ene9ba/IoT-3D-Printer-Control/Hardware/Cabinetcontrol1/Step/IRLML2402TRPBF.stp

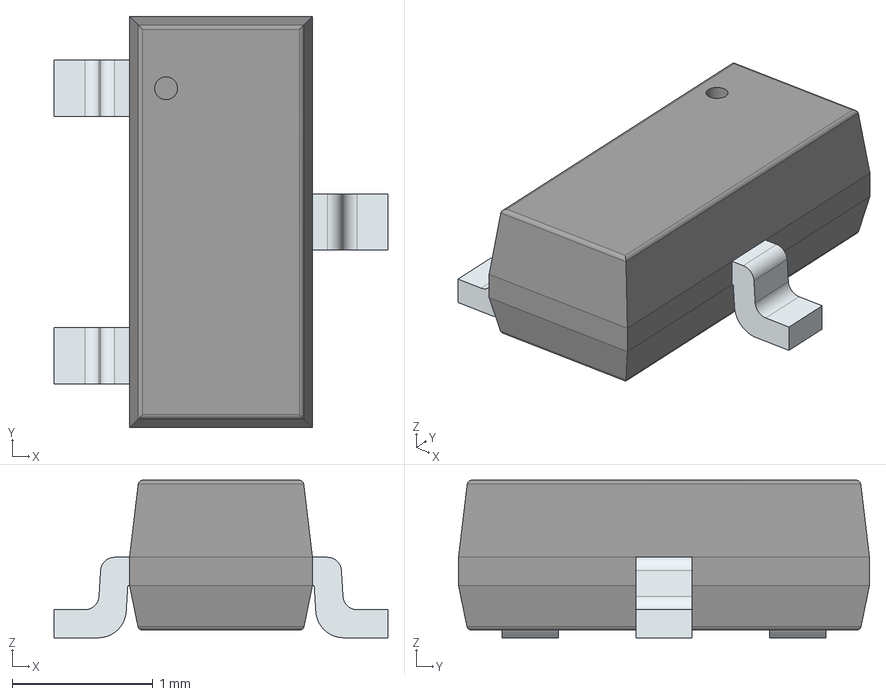
[picture p22: CAD file, 2024-01-27]
Hardware/Cabinetcontrol1/Step/IRLML2402TRPBF.stp
2.37 x 2.92 x 1.12 mm
PinsArrayL
FilletPinR
