ene9ba/IoT-3D-Printer-Control/Hardware/Cabinetcontrol1/Step/Phoenix-5,08-2pol.stp

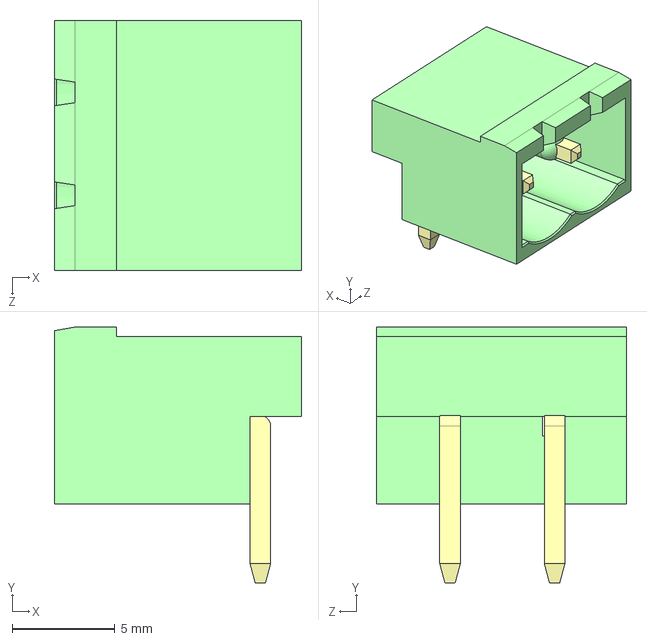
[picture p23: CAD file, 2024-01-27]
Hardware/Cabinetcontrol1/Step/Phoenix-5,08-2pol.stp
12.0 x 12.4 x 12.2 mm
